DPTPSystem/WandText/Program/abc.c

//A B C D E F G H I J K L M N O P Q R S T U V W X Y Z 0 1 2 3 4 5 6 7 8 9 - : .
static const unsigned char ABC[40][7] ={{0b00000,//A
    0b01110,
    0b10001,
    0b10001,
    0b11111,
    0b10001,
    0b10001},
    {0b00000,//B
        0b11110,
        0b10001,
        0b11110,
        0b10001,
        0b10001,
        0b11110},
    
    {0b00000,//C
        0b01110,
        0b10001,
        0b10000,
        0b10000,
        0b10001,
        0b01110},
    
    {0b00000,//D
        0b11110,
        0b10001,
        0b10001,
        0b10001,
        0b10001,
        0b11110},
    
    {0b00000,//E
        0b11111,
        0b10000,
        0b11100,
        0b10000,
        0b10000,
        0b11111},
    
    {0b00000,//F
        0b11111,
        0b10000,
        0b11100,
        0b10000,
        0b10000,
        0b10000},
    
    {0b00000,//G
        0b01111,
        0b10000,
        0b10111,
        0b10101,
        0b10001,
        0b01110},
    
    {0b00000,//H
        0b10001,
        0b10001,
        0b11111,
        0b10001,
        0b10001,
        0b10001},
    
    {0b00000,//I
        0b01110,
        0b00100,
        0b00100,
        0b00100,
        0b00100,
        0b01110},
    
    {0b00000,//J
        0b00111,
        0b00001,
        0b00001,
        0b00001,
        0b10001,
        0b01110},
    
    {0b00000,//K
        0b10001,
        0b10010,
        0b11100,
        0b10100,
        0b10010,
        0b10001},
    
    {0b00000,//L
        0b10000,
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
        0b00100,
        0b00000},
    
    {0b00000,//.
        0b00000,
        0b00000,
        0b00000,
        0b00000,
        0b00000,
        0b00001},
    
    {0b00000,// (szóköz)
        0b00000,
        0b00000,
        0b00000,
        0b00000,
        0b00000,
        0b00000}
};
